ysoldak/fpvc-target/media/Inside.jpg

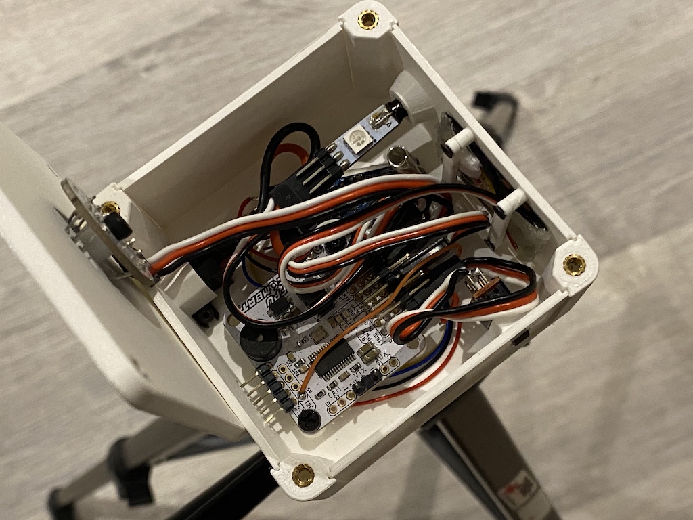
media/Inside.jpg
