ysoldak/fpvc-target/media/Assembly.png

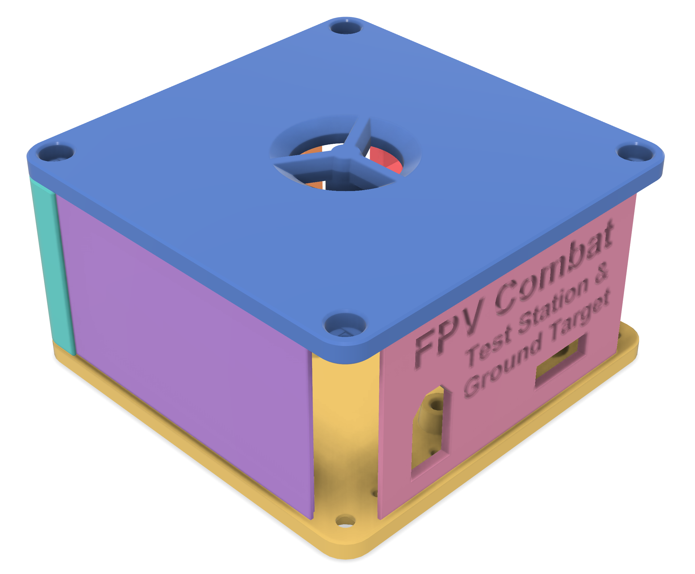
media/Assembly.png
