ysoldak/fpvc-target/media/Wiring.jpg

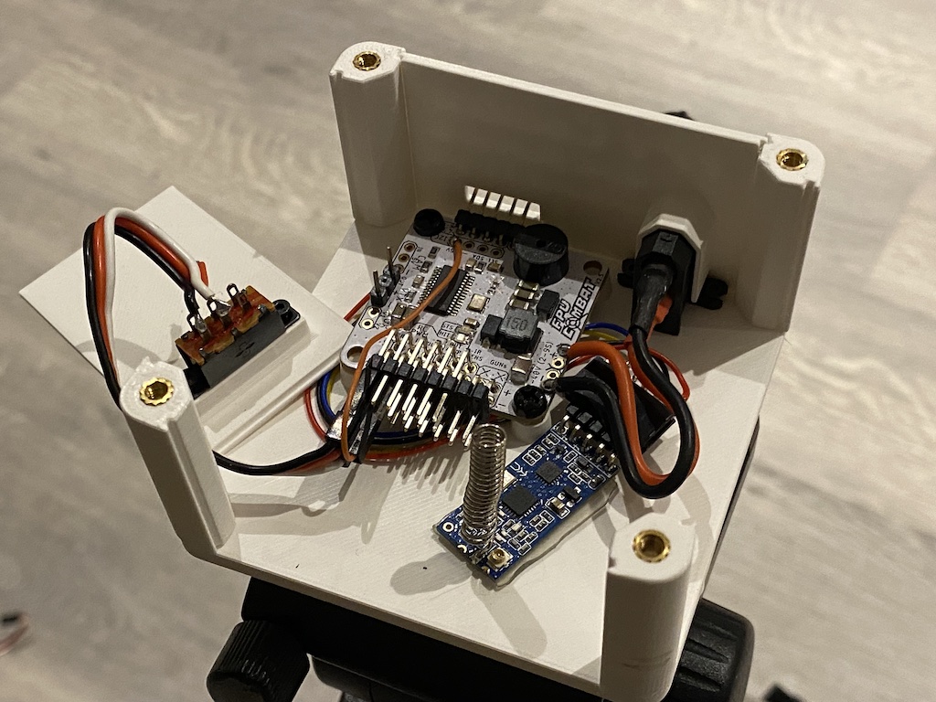
media/Wiring.jpg
